skoya/wind-tunnel/exports/airflow/side_slice_through_centre_gap.png

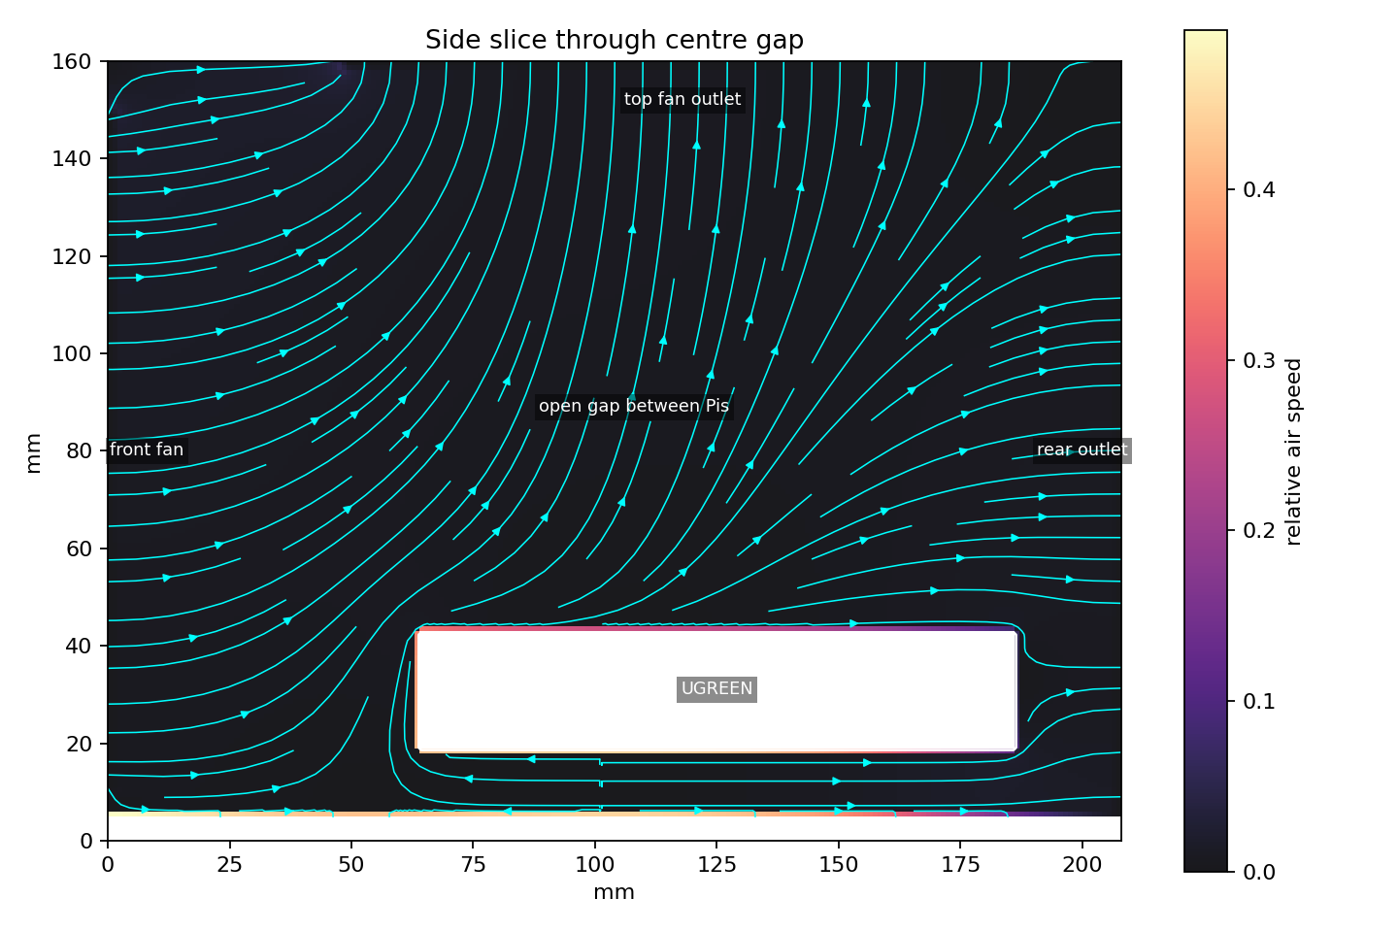
exports/airflow/side_slice_through_centre_gap.png
