skoya/wind-tunnel/exports/airflow/side_slice_through_centre_gap_vented_ugreen.png

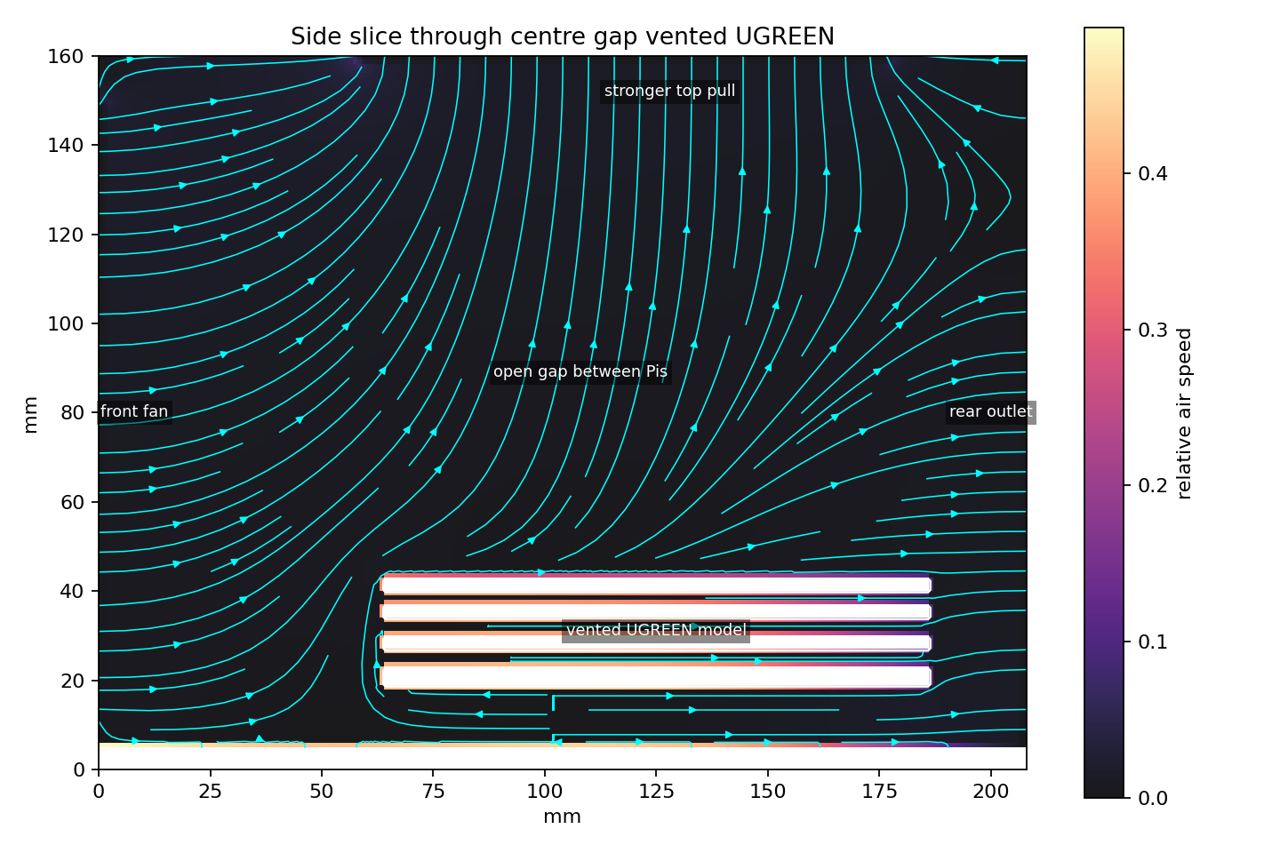
exports/airflow/side_slice_through_centre_gap_vented_ugreen.png
