skoya/wind-tunnel/exports/airflow/side_slice_through_pi_stack_solid_ugreen.png

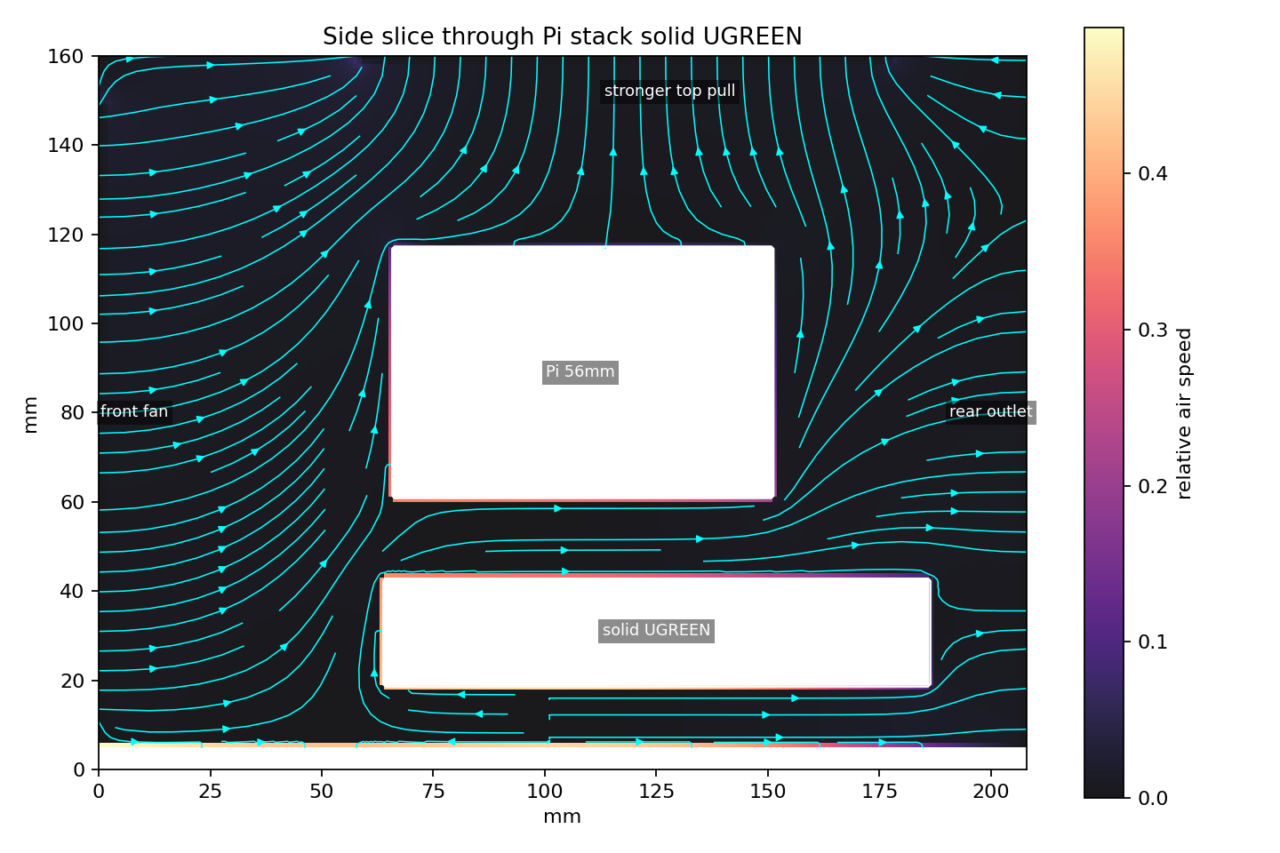
exports/airflow/side_slice_through_pi_stack_solid_ugreen.png
