skoya/wind-tunnel/exports/mac_upper_cooler_preview.stl

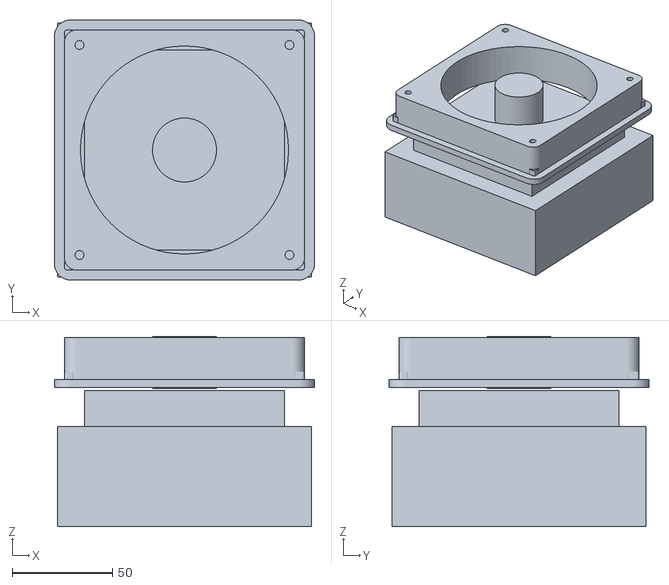
[picture p23: CAD file, 2026-05-08]
exports/mac_upper_cooler_preview.stl
130.0 x 130.0 x 95.0
