skoya/wind-tunnel/exports/pi_frame_bridge.stl

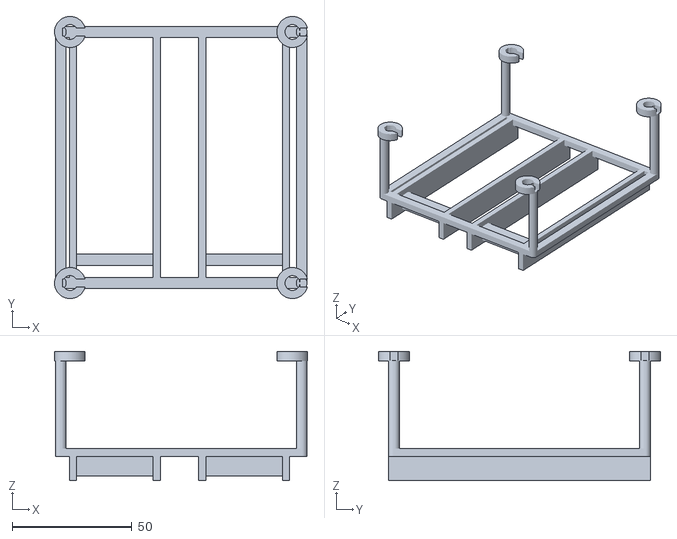
[picture p24: CAD file, 2026-05-08]
exports/pi_frame_bridge.stl
105.8 x 118.0 x 54.0
