skoya/wind-tunnel/surface-pro-9-cooling-stand/front_lip_v4.stl

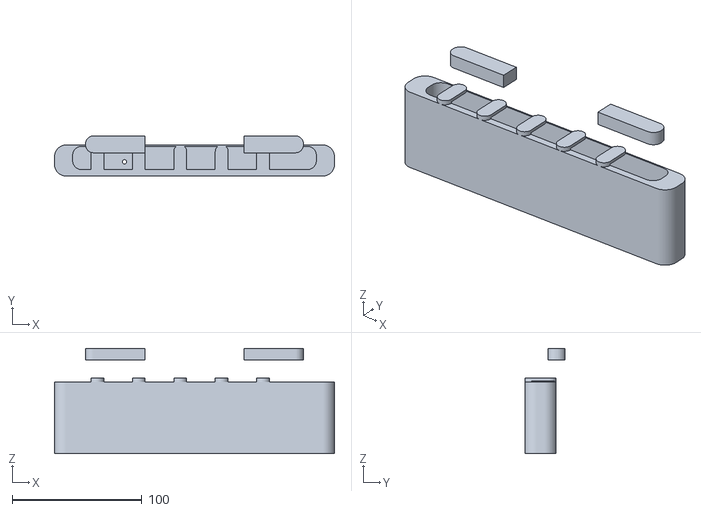
[picture p25: CAD file, 2026-05-12]
surface-pro-9-cooling-stand/front_lip_v4.stl
216.0 x 31.0 x 81.2
