skoya/wind-tunnel/exports/cable_route_ghosts.stl

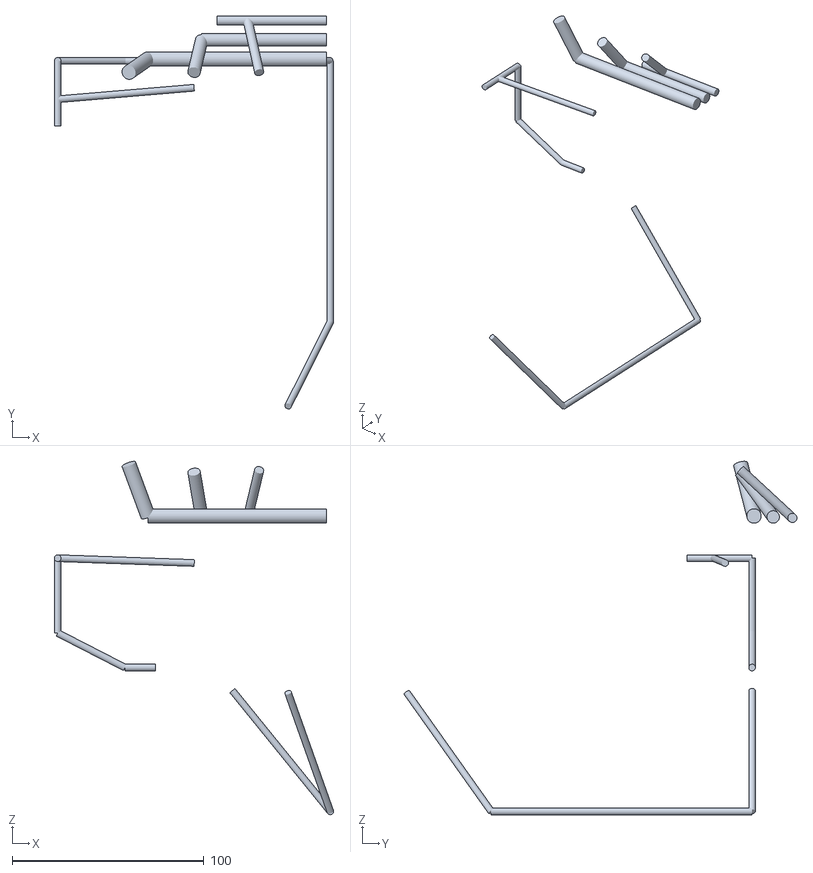
[picture p26: CAD file, 2026-05-07]
exports/cable_route_ghosts.stl
145.6 x 204.9 x 184.3
