skoya/wind-tunnel/surface-pro-9-cooling-stand/printable_frame_v4.stl

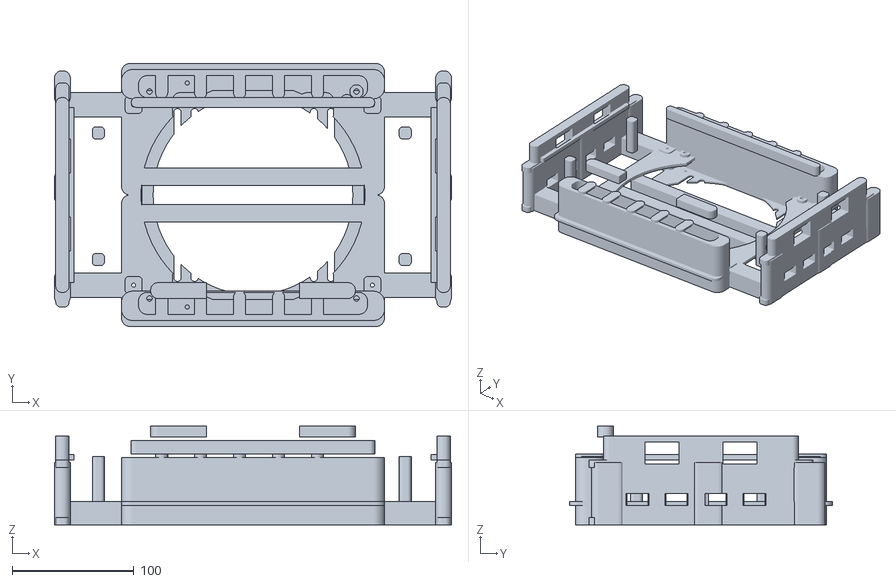
[picture p27: CAD file, 2026-05-12]
surface-pro-9-cooling-stand/printable_frame_v4.stl
326.0 x 216.0 x 81.2
