skoya/wind-tunnel/exports/pi_cassette_left.stl

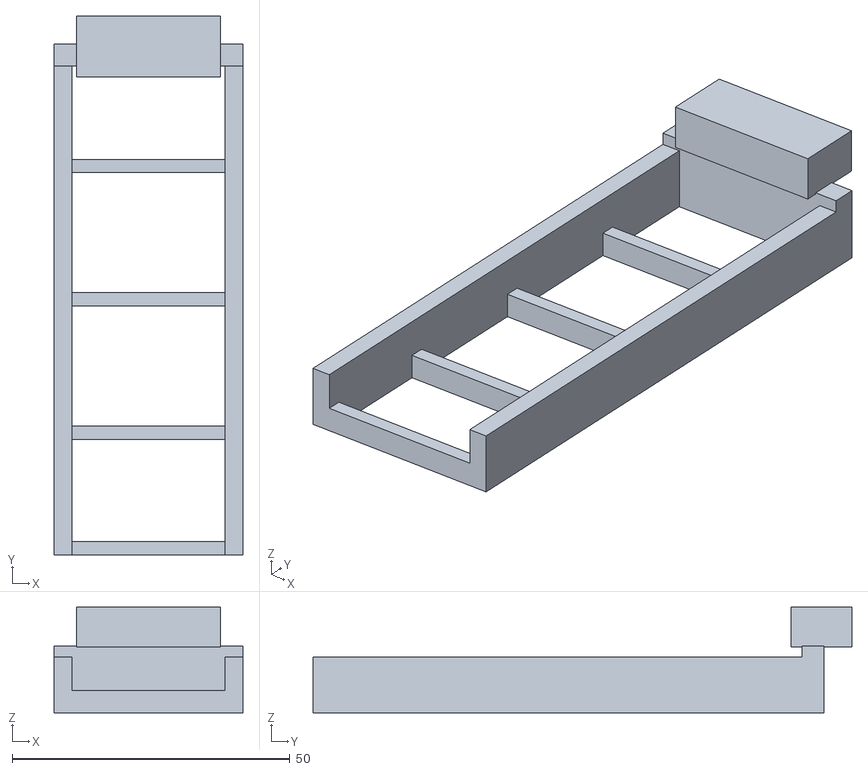
[picture p28: CAD file, 2026-05-07]
exports/pi_cassette_left.stl
34.0 x 97.0 x 19.0
