skoya/wind-tunnel/exports/front_fan_cassette_body.stl

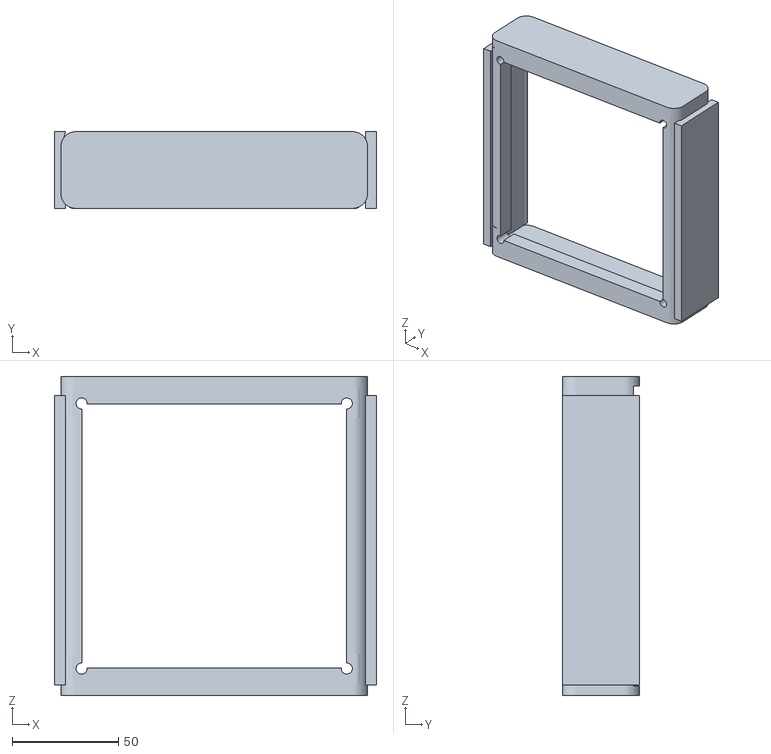
[picture p29: CAD file, 2026-05-06]
exports/front_fan_cassette_body.stl
151.2 x 36.0 x 150.0
