skoya/wind-tunnel/exports/front_cassette_with_grille.stl

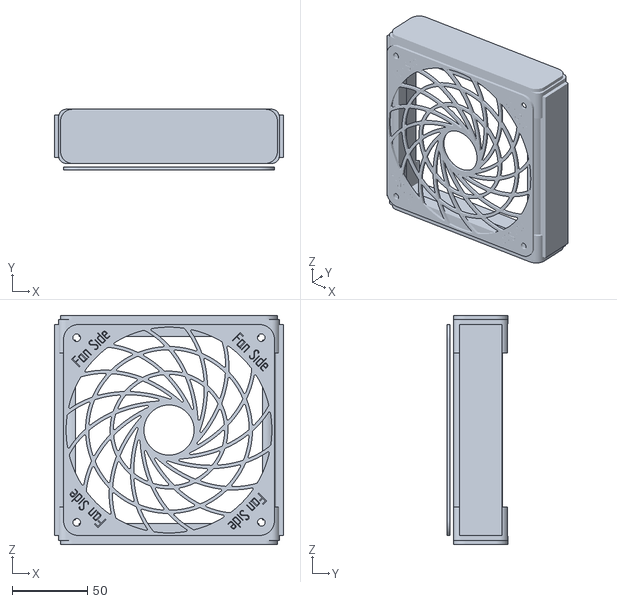
[picture p30: CAD file, 2026-05-06]
exports/front_cassette_with_grille.stl
152.0 x 40.2 x 152.0
