skoya/wind-tunnel/exports/front_noctua_grille.stl

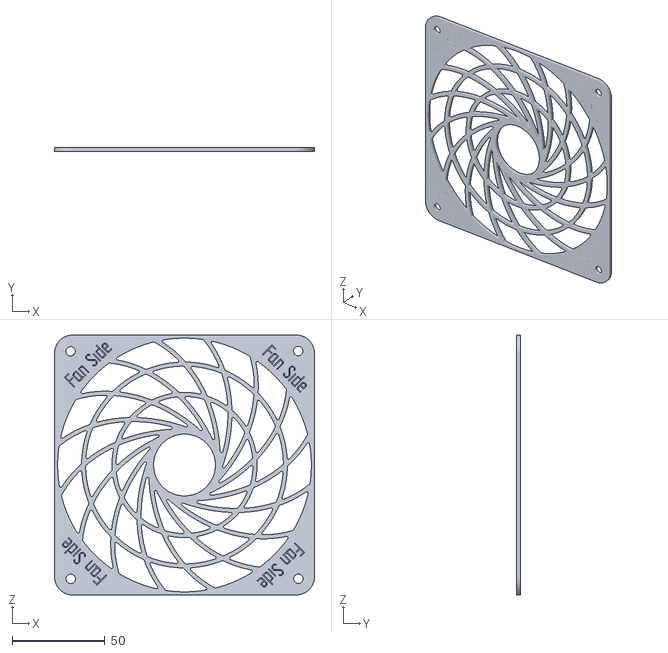
[picture p31: CAD file, 2026-05-06]
exports/front_noctua_grille.stl
140.0 x 2.00 x 140.0
